TeXitoi/keyseebee/cad/plate.2d.scad

use <functions.scad>

plate();
